Nathan-Mossaad/ftpm-glitcher/wiring/wiring.kicad_sch

## KiCad design wiring/wiring.kicad_sch (2026-07-19)

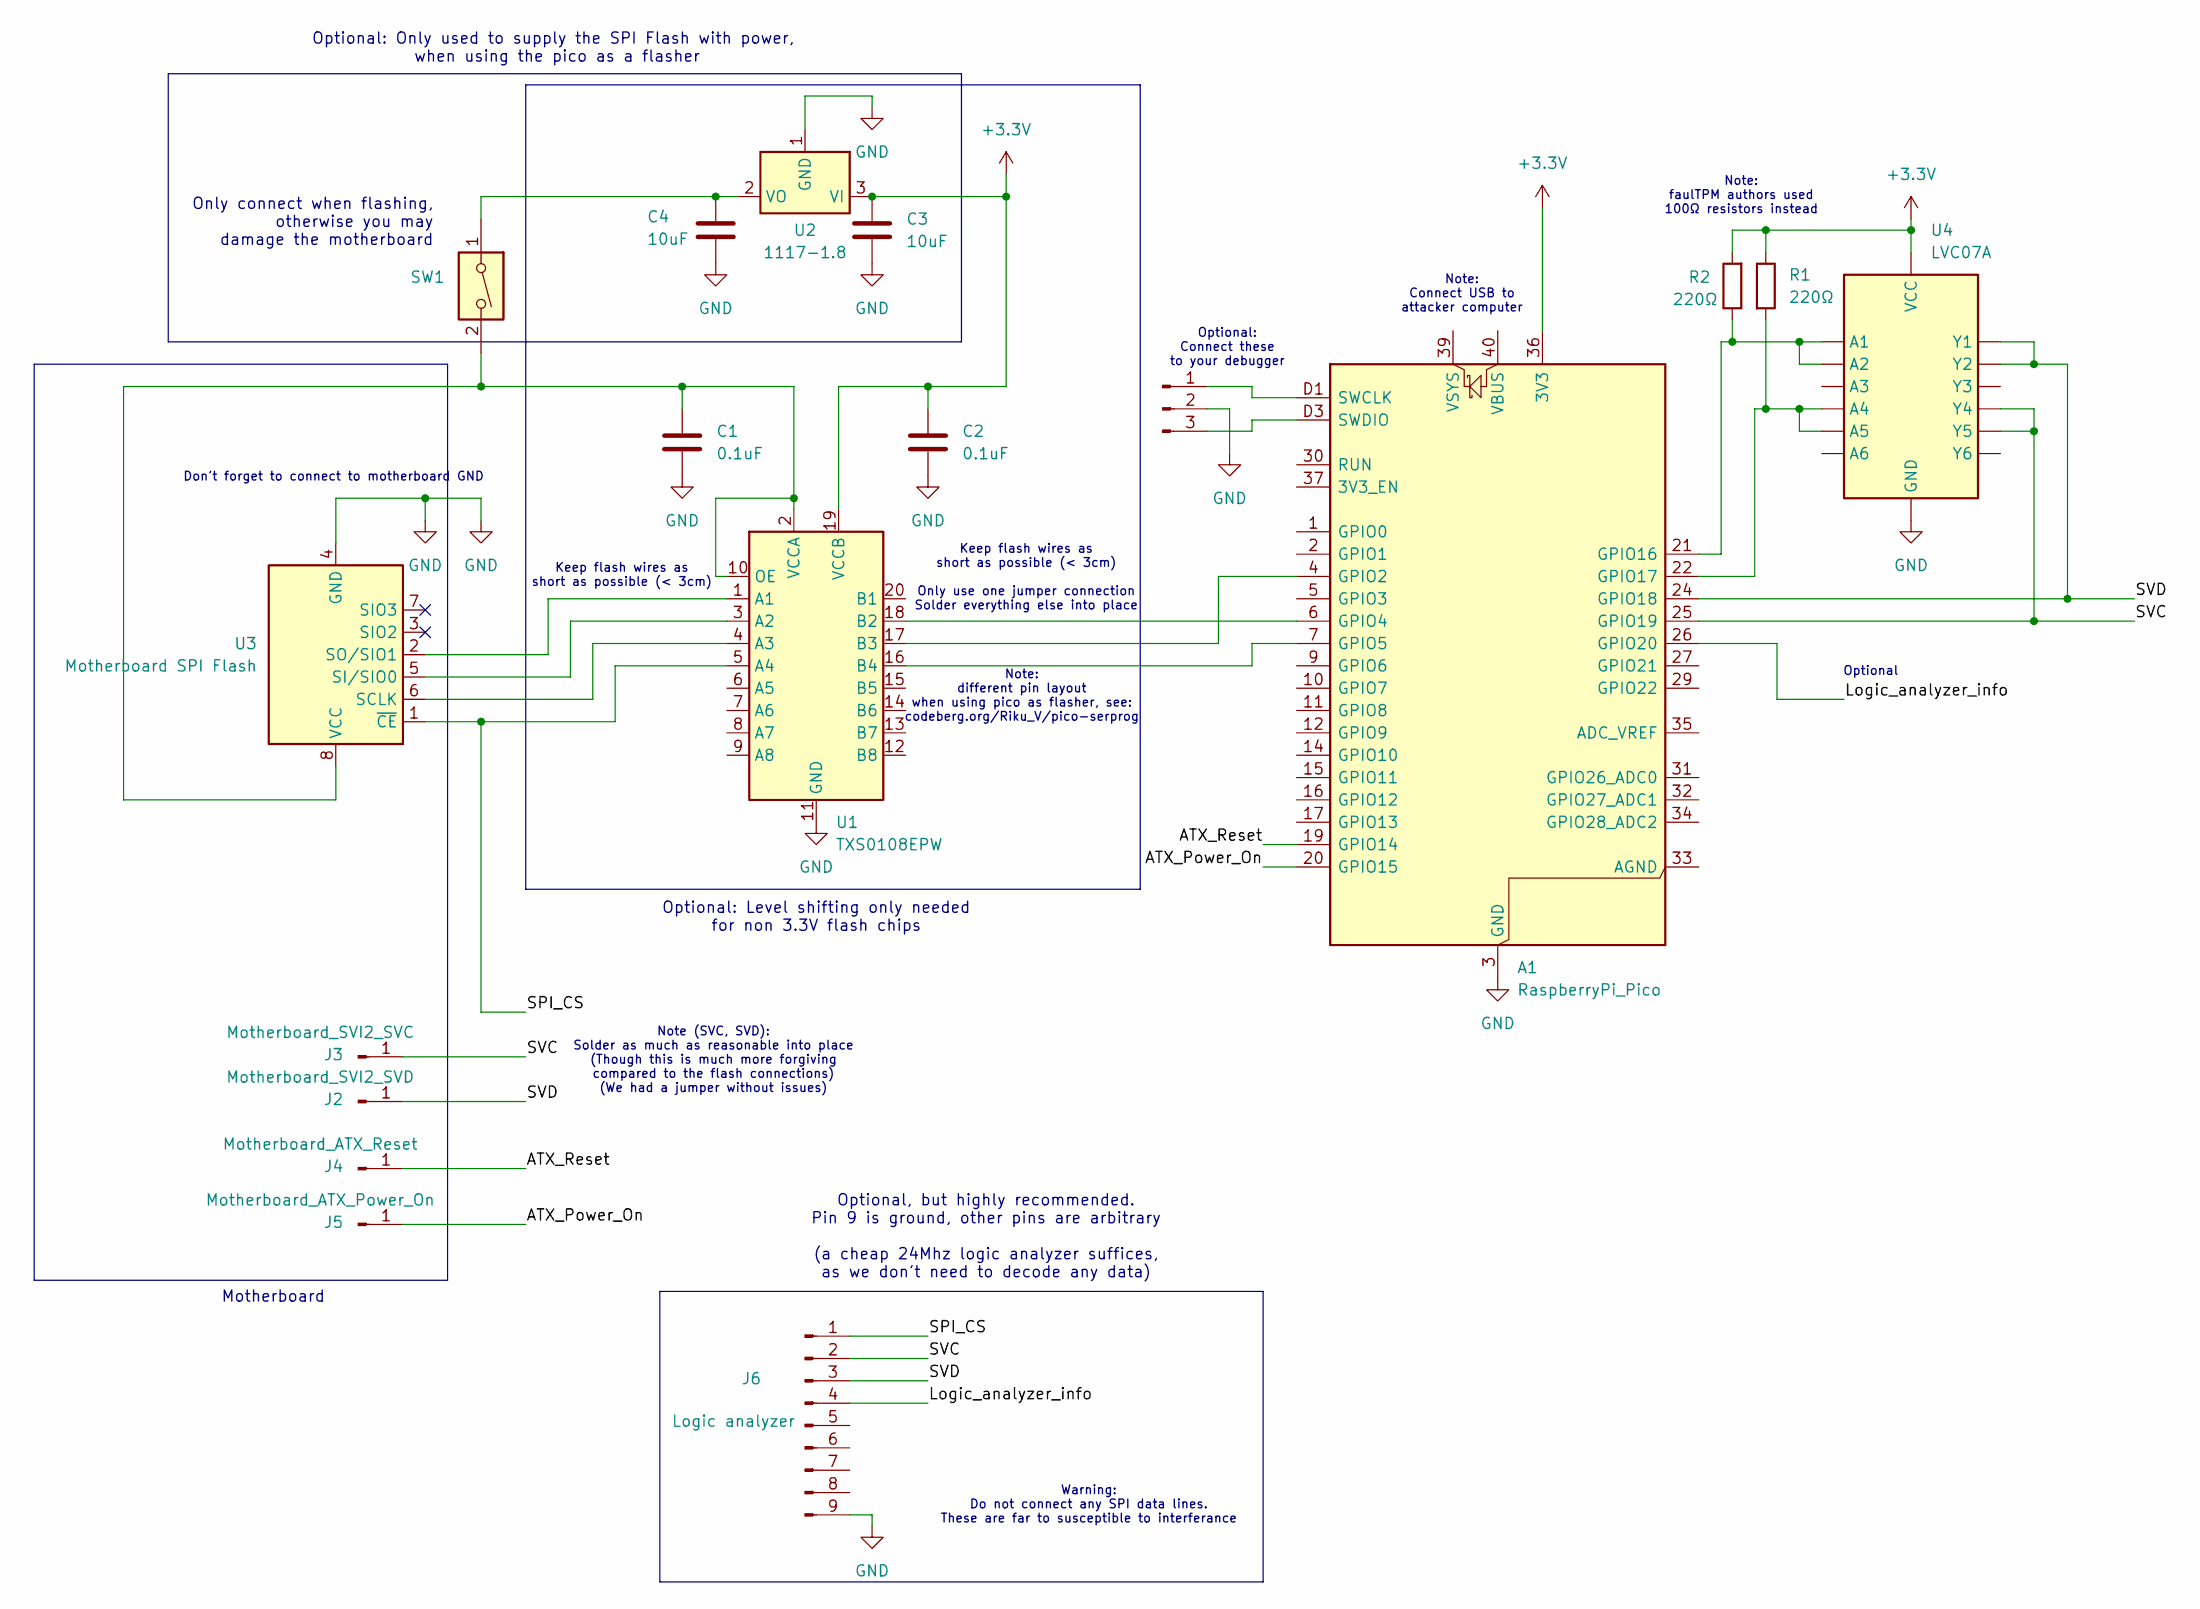
[picture p3: schematic wiring.kicad_sch]

Parts:
A1: RaspberryPi_Pico; RaspberryPi_Pico_SMD_HandSolder
C1, C2: 0.1uF
C3, C4: 10uF
J1: Conn_01x03_Pin
J2: Motherboard_SVI2_SVD
J3: Motherboard_SVI2_SVC
J4: Motherboard_ATX_Reset
J5: Motherboard_ATX_Power_On
J6: Logic analyzer
R1, R2: 220Ω
SW1: SW_DIP_x01
U1: TXS0108EPW; TSSOP-20_4.4x6.5mm_P0.65mm
U2: 1117-1.8; SOT-223-3_TabPin2
U3: Motherboard SPI Flash; Winbond_USON-8-1EP_3x2mm_P0.5mm_EP0.2x1.6mm
U4: LVC07A

Connections:
+3.3V: A1.36 (3V3), C2.1, C3.1, R1.1, R2.2, U1.19 (VCCB), U2.3 (VI), U4.
ATX_Power_On: A1.20 (GPIO15), J5.1
ATX_Reset: A1.19 (GPIO14), J4.1
GND: A1.3 (GND), A1.8 (GND), A1.13 (GND), A1.18 (GND), A1.23 (GND), A1.28 (GND), A1.38 (GND), A1.D2 (GND), C1.2, C2.2, C3.2, C4.2, J1.2, J6.9, U1.11 (GND), U2.1 (GND), U3.4 (GND), U4.
Logic_analyzer_info: A1.26 (GPIO20), J6.4
unnamed: A1.4 (GPIO2), U1.17 (B3)
unnamed: A1.6 (GPIO4), U1.18 (B2)
unnamed: A1.7 (GPIO5), U1.16 (B4)
unnamed: A1.21 (GPIO16), R2.1, U4.
unnamed: A1.22 (GPIO17), R1.2, U4.
unnamed: A1.D1 (SWCLK), J1.1
unnamed: A1.D3 (SWDIO), J1.3
unnamed: C1.1, SW1.2, U1.2 (VCCA), U1.10 (OE), U3.8 (VCC)
unnamed: C4.1, SW1.1, U2.2 (VO)
unnamed: U1.1 (A1), U3.2 (SO/SIO1)
unnamed: U1.3 (A2), U3.5 (SI/SIO0)
unnamed: U1.4 (A3), U3.6 (SCLK)
SPI_CS: J6.1, U1.5 (A4), U3.1 (~CE)
SVC: A1.25 (GPIO19), J3.1, J6.2, U4.
SVD: A1.24 (GPIO18), J2.1, J6.3, U4.

Notes on the sheet:
Keep flash wires as short as possible (< 3cm)
Keep flash wires as short as possible (< 3cm) Only use one jumper connection Solder everything else into place
Note: faulTPM authors used 100Ω resistors instead
Optional
Optional: Only used to supply the SPI Flash with power, when using the pico as a flasher
Note: different pin layout when using pico as flasher, see: codeberg.org/Riku_V/pico-serprog
Optional: Level shifting only needed for non 3.3V flash chips
Optional: Connect these to your debugger
Optional, but highly recommended. Pin 9 is ground, other pins are arbitrary (a cheap 24Mhz logic analyzer suffices, as we don't need to decode any data)
Don't forget to connect to motherboard GND
Motherboard
Note: Connect USB to attacker computer
Warning: Do not connect any SPI data lines. These are far to susceptible to interferance
Only connect when flashing, otherwise you may damage the motherboard
Note (SVC, SVD): Solder as much as reasonable into place (Though this is much more forgiving compared to the flash connections) (We had a jumper without issues)
