Nathan-Mossaad/ftpm-glitcher/glitcher-pc/src/cli.rs

use std::path::PathBuf;

use clap::{Parser, Subcommand};
use clap_complete::Shell;

#[derive(Debug, Parser)]
#[command(name = "glitcher", about = "Control the glitcher")]
pub struct Cli {
    /// Serial port connected to the controller.
    #[arg(long, global = true, default_value = "/dev/ttyACM0")]
    pub port: PathBuf,

    #[command(subcommand)]
    pub command: Command,
}

#[derive(Debug, Subcommand)]
pub enum Command {
    /// Send a ping to the controller.
    Ping,

    /// Check that the Pico firmware matches this application's version.
    CheckVersion,

    /// Reboot the Pico controller.
    Reboot,

    /// Pulse the target reset line without rebooting the Pico controller.
    RebootTarget,

    /// Hold the target's power button down.
    PressPowerButton {
        /// Duration to hold the power button, in milliseconds.
        #[arg(long, value_parser = clap::value_parser!(u32).range(1..), default_value_t = 500)]
        duration_ms: u32,
    },

    /// Count chip-select falling edges, default 1s.
    CountChipSelects {
        #[arg(default_value_t = 1)]
        timeout_s: u32,

        /// Reboot the target before counting chip-select edges.
        #[arg(long)]
        reboot: bool,
    },

    /// Capture a single SPI0 transaction (up to 128 KiB).
    TapSpi {
        /// Number of bytes to capture (1 through 131072).
        #[arg(long, default_value_t = 32, value_parser = clap::value_parser!(u32).range(1..=131072))]
        byte_count: u32,

        /// Seconds to wait for the transaction.
        #[arg(long, default_value_t = 1)]
        timeout_s: u32,

        /// Reboot the target before capturing the transaction.
        #[arg(long)]
        reboot: bool,
    },

    /// Set both SVI2 rails to a raw VID, or use the original default VIDs.
    SetVid {
        /// Raw eight-bit VID (0 through 255). Omit to use the original VSoc and VCore defaults.
        #[arg(value_parser = clap::value_parser!(u8).range(0..=255))]
        vid: Option<u8>,
    },

    /// Wait for GPIO18 to become high, then disable SVI2 telemetry.
    DisableTelemetry {
        /// Seconds to wait for GPIO18 to become high.
        #[arg(long, default_value_t = 1000)]
        timeout_ms: u64,

        /// Reboot the target after telemetry is disabled.
        #[arg(long)]
        reboot: bool,
    },

    /// Run a voltage glitch attack.
    Attack {
        /// Number of SPI bytes to capture (1 through 131072).
        #[arg(long, default_value_t = 4096, value_parser = clap::value_parser!(u32).range(1..=131072))]
        spi_byte_count: u32,

        /// Raw eight-bit VID. Omit to use the controller default VIDs.
        #[arg(long, default_value_t = 0xC0,value_parser = clap::value_parser!(u8).range(0..=255))]
        vid: u8,

        /// Chip-select falling-edge count that triggers the glitch.
        #[arg(long)]
        chip_select_count: u32,

        /// Delay after the trigger before dipping the voltage, in nanoseconds.
        #[arg(long)]
        wait_duration_ns: u32,

        /// Voltage-dip duration, in nanoseconds.
        #[arg(long)]
        dip_duration_ns: u32,
    },

    /// Write shell completions to standard output.
    GenerateCompletions {
        /// Shell to generate completions for.
        #[arg(value_enum, default_value_t = Shell::Bash)]
        shell: Shell,
    },
}
