Nathan-Mossaad/ftpm-glitcher/glitcher-rpc/src/lib.rs

#![no_std]

pub use postcard;

use serde::{Deserialize, Serialize};

/// The largest SPI transaction the tap currently captures.
pub const SPI_TAP_MAX_BYTES: usize = 128 * 1024;

/// Capture data carried in one USB/RPC response frame.
///
/// This leaves room for the RPC envelope and COBS framing in a 64-byte USB
/// full-speed packet.
pub const CHUNK_BYTES: usize = 32;

#[derive(Debug, Clone, Copy, PartialEq, Eq, Serialize, Deserialize)]
#[cfg_attr(feature = "mcu", derive(defmt::Format))]
pub enum ChunkStatus {
    Complete,
    TimedOut,
}

/// One frame of a generic chunked RPC transfer.
#[derive(Debug, Clone, Copy, PartialEq, Eq, Serialize, Deserialize)]
#[cfg_attr(feature = "mcu", derive(defmt::Format))]
pub struct Chunk {
    pub offset: u32,
    pub data: [u8; CHUNK_BYTES],
    pub byte_count: u8,
    pub is_last: bool,
    /// Meaningful on the final chunk.
    pub status: ChunkStatus,
}

#[derive(Debug, Clone, Copy, PartialEq, Eq, Serialize, Deserialize)]
#[cfg_attr(feature = "mcu", derive(defmt::Format))]
pub enum SpiTapError {
    InvalidByteCount,
    ReadFailed,
}

#[derive(Debug, Clone, Copy, PartialEq, Eq, Serialize, Deserialize)]
#[cfg_attr(feature = "mcu", derive(defmt::Format))]
pub enum Svi2Error {
    WriteFailed,
}

impl core::fmt::Display for Svi2Error {
    fn fmt(&self, f: &mut core::fmt::Formatter<'_>) -> core::fmt::Result {
        match self {
            Self::WriteFailed => write!(f, "I2C write to the SVI2 controller failed"),
        }
    }
}

impl core::fmt::Display for SpiTapError {
    fn fmt(&self, f: &mut core::fmt::Formatter<'_>) -> core::fmt::Result {
        match self {
            Self::InvalidByteCount => {
                write!(f, "byte count must be between 1 and {SPI_TAP_MAX_BYTES}")
            }
            Self::ReadFailed => write!(f, "SPI read failed"),
        }
    }
}

#[derive(Debug, Clone, Copy, PartialEq, Eq, Serialize, Deserialize)]
#[cfg_attr(feature = "mcu", derive(defmt::Format))]
pub struct RpcMessage<T> {
    pub id: u32,
    pub message: T,
}

#[derive(Debug, Clone, Copy, PartialEq, Eq, Serialize, Deserialize)]
#[cfg_attr(feature = "mcu", derive(defmt::Format))]
pub struct FirmwareVersion {
    pub major: u16,
    pub minor: u16,
    pub patch: u16,
}

impl core::fmt::Display for FirmwareVersion {
    fn fmt(&self, f: &mut core::fmt::Formatter<'_>) -> core::fmt::Result {
        write!(f, "{}.{}.{}", self.major, self.minor, self.patch)
    }
}

// The parent package for all host to controller communication
#[derive(Debug, Clone, Copy, PartialEq, Serialize, Deserialize)]
#[cfg_attr(feature = "mcu", derive(defmt::Format))]
pub enum Host2ControllerMessage {
    Ping,
    GetVersion,
    Reboot,
    /// Pull GP15 low for 1 ms to reboot the target without resetting the controller.
    RebootTarget,
    /// Count chip-select falling edges for the requested duration.
    CountChipSelects {
        timeout_s: u32,
        reboot: bool,
    },
    /// Capture one SPI0 slave transaction. `byte_count` must be 1..=131072.
    TapSpi {
        byte_count: u32,
        timeout_s: u32,
        reboot: bool,
    },
    /// Set both SVI2 rails to a raw VID, or apply the Teensy firmware defaults.
    SetVid {
        /// A raw eight-bit VID. `None` selects the original default VIDs.
        vid: Option<u8>,
    },
    /// Wait for GPIO18 to become high, then disable SVI2 telemetry and optionally reboot the target.
    DisableTelemetry {
        timeout_ms: u64,
        reboot: bool,
    },
    /// Pull GP14 low for the requested duration to press the target's power button.
    PressPowerButton {
        duration_ms: u32,
    },
    /// Run a configured voltage glitch attack.
    GlitchAttack {
        spi_byte_count: u32,
        vid: u8,
        chip_select_count: u32,
        wait_duration_ns: u32,
        dip_duration_ns: u32,
    },
}

// The parent package for all controller to host communication
#[derive(Debug, Clone, Copy, PartialEq, Serialize, Deserialize)]
#[cfg_attr(feature = "mcu", derive(defmt::Format))]
pub enum Controller2HostMessage {
    UnknownCommand,
    Pong,
    Rebooting,
    Version(FirmwareVersion),
    ChipSelectCount(u32),
    Chunk(Chunk),
    SpiTapError(SpiTapError),
    VidSet,
    TelemetryDisabled,
    TelemetryTimedOut,
    Svi2Error(Svi2Error),
    TargetRebooted,
    PowerButtonPressed,
    GlitchAttackSucceeded,
    GlitchAttackFailed,
    GlitchAttackFailedTargetNotRunning,
}
